probity-2-0/rover-hardware/jude-mechanical designs/rare wheel suspension.SLDASM

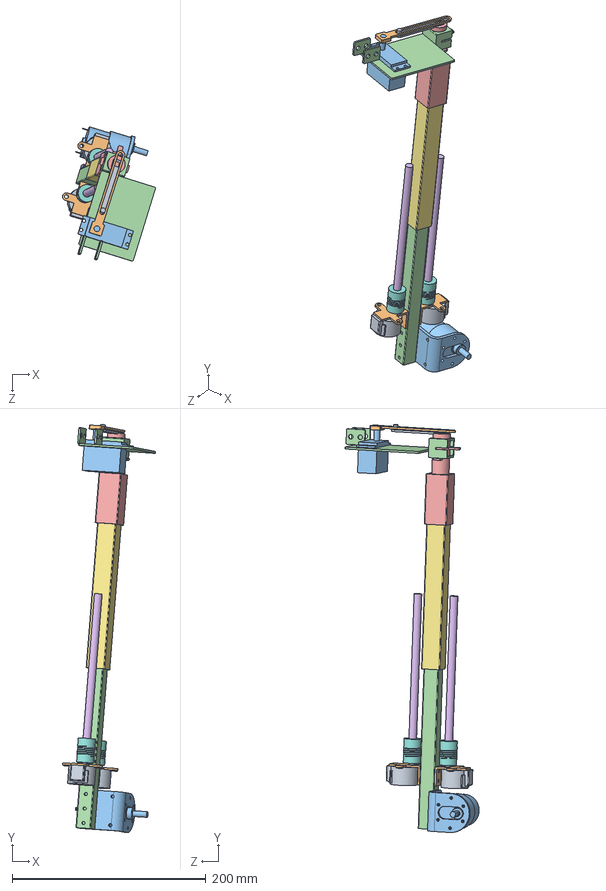
[picture p19: CAD file, 2026-03-30]
jude-mechanical designs/rare wheel suspension.SLDASM
96.2 x 421.2 x 138.8 mm
16mm inner tube
motor-bracket combined
suspension stepper bracket x 2
byj28--48 x 2
5to8 flexible coupler x 2
20mmsteel tube
suspension pin x 2
servo whee suspension connector cup
servo rotation strength fixture-rare
my_mg996r
slider pin
suspension rotary pin
