probity-2-0/rover-hardware/jude-mechanical designs/right full assembly.SLDASM

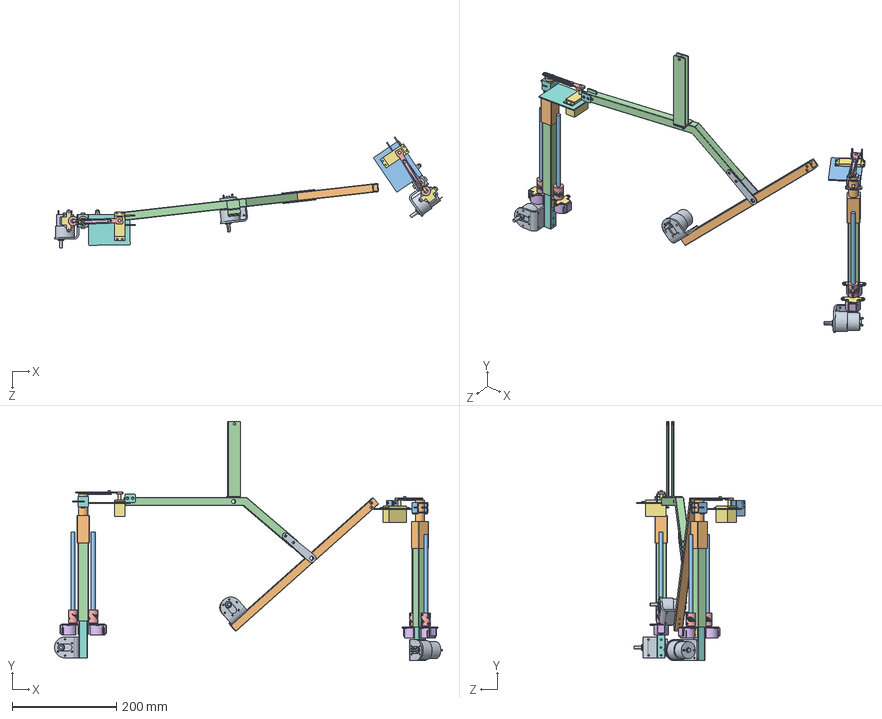
[picture p20: CAD file, 2026-03-30]
jude-mechanical designs/right full assembly.SLDASM
745.0 x 459.7 x 213.8 mm
16mm inner tube x 2
suspension stepper bracket x 4
byj28--48 x 4
5to8 flexible coupler x 4
20mmsteel tube x 2
suspension pin x 4
servo whee suspension connector cup x 2
motor-bracket combined x 3
servo rotation strength fixture-rare mirror
my_mg996r x 2
suspension rotary pin x 2
slider pin x 2
rare middle part mirror
servo rotation strength fixture mirror
middle16mm
connection bracket x 2
