probity-2-0/rover-hardware/jude-mechanical designs/assembled servo  system.SLDASM

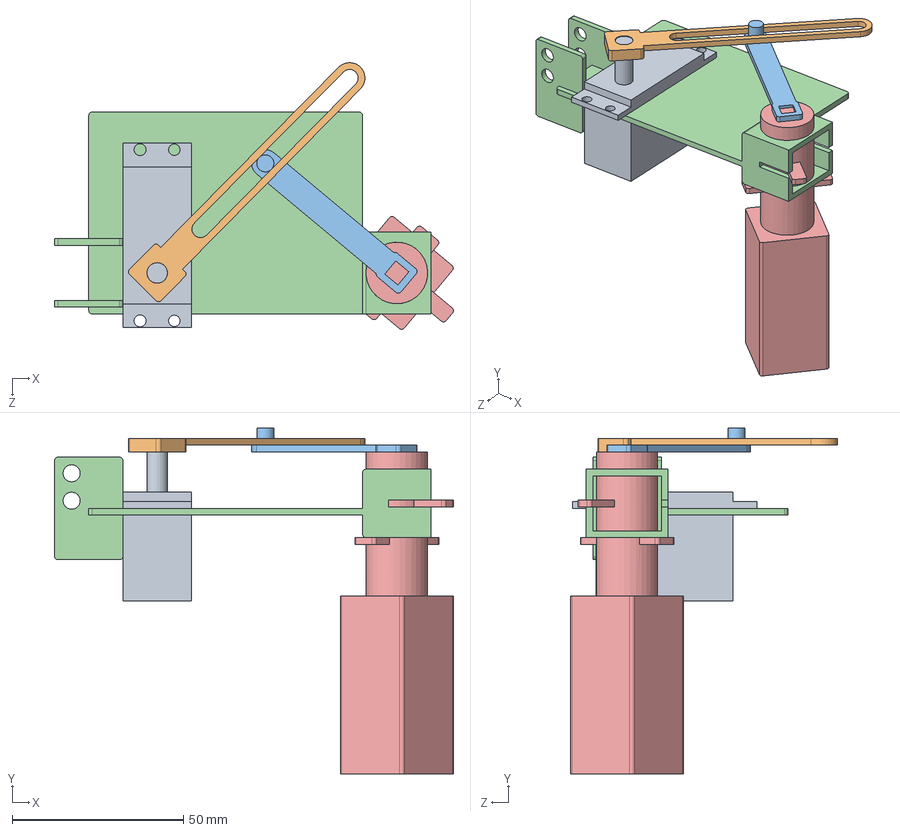
[picture p21: CAD file, 2026-03-30]
jude-mechanical designs/assembled servo system.SLDASM
116.6 x 101.0 x 77.9 mm
servo whee suspension connector cup
servo rotation strength fixture
suspension rotary pin
slider pin
my_mg996r
