probity-2-0/rover-hardware/jude-mechanical designs/middle16mm.SLDPRT

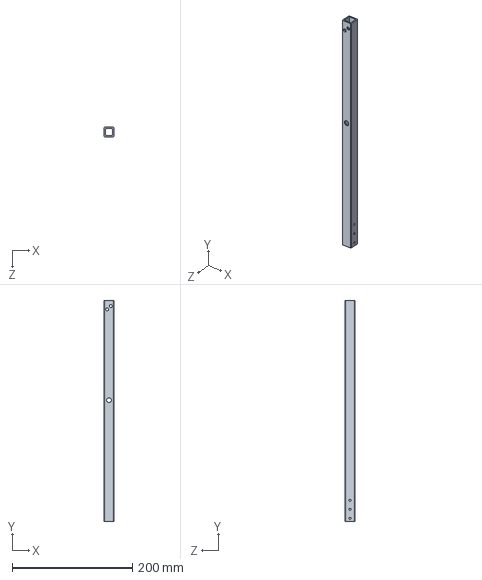
[picture p29: CAD file, 2026-03-30]
jude-mechanical designs/middle16mm.SLDPRT
16.0 x 368.0 x 16.0 mm
