probity-2-0/rover-hardware/jude-mechanical designs/JGB37-520-12v-319RPM.SLDPRT

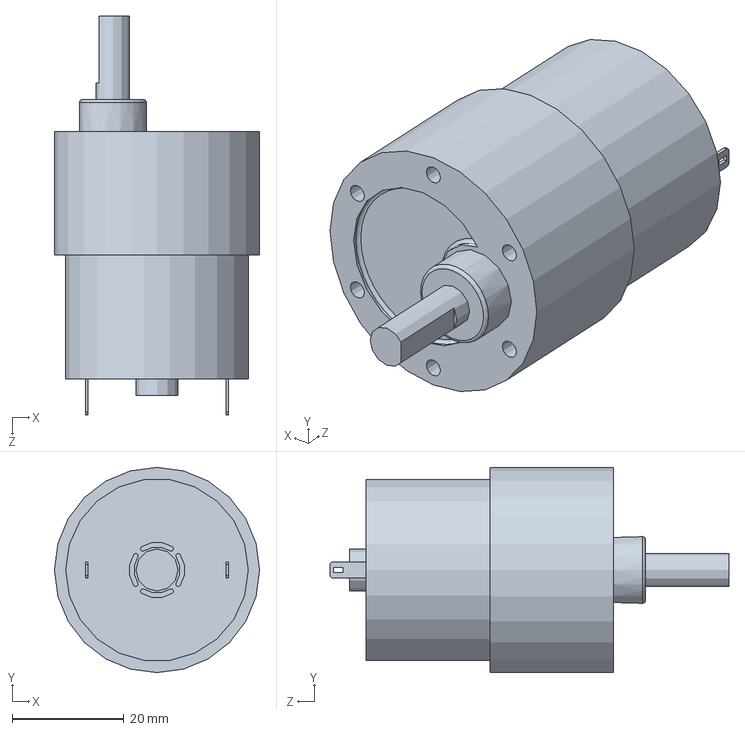
[picture p30: CAD file, 2026-03-30]
jude-mechanical designs/JGB37-520-12v-319RPM.SLDPRT
36.8 x 36.8 x 71.5 mm
