probity-2-0/rover-hardware/jude-mechanical designs/body width member.SLDPRT

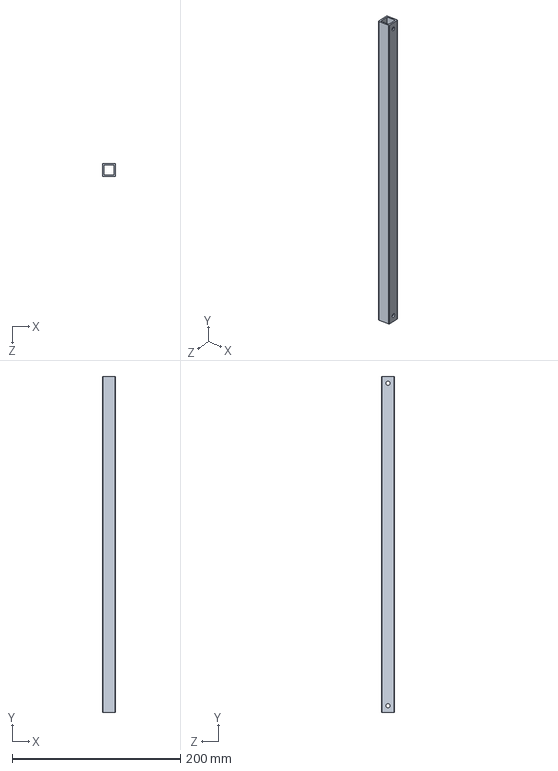
[picture p31: CAD file, 2026-03-30]
jude-mechanical designs/body width member.SLDPRT
16.0 x 400.0 x 16.0 mm
