probity-2-0/rover-hardware/jude-mechanical designs/suspension bracket.SLDPRT

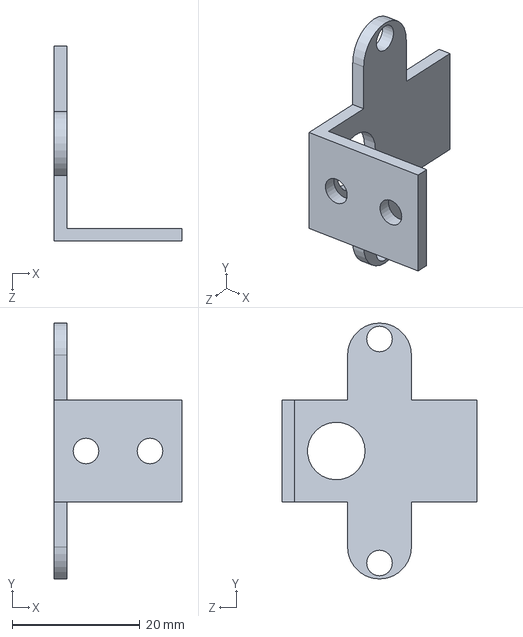
[picture p32: CAD file, 2026-03-30]
jude-mechanical designs/suspension bracket.SLDPRT
20.0 x 40.0 x 30.5 mm
