probity-2-0/rover-hardware/jude-mechanical designs/button  frame.SLDPRT

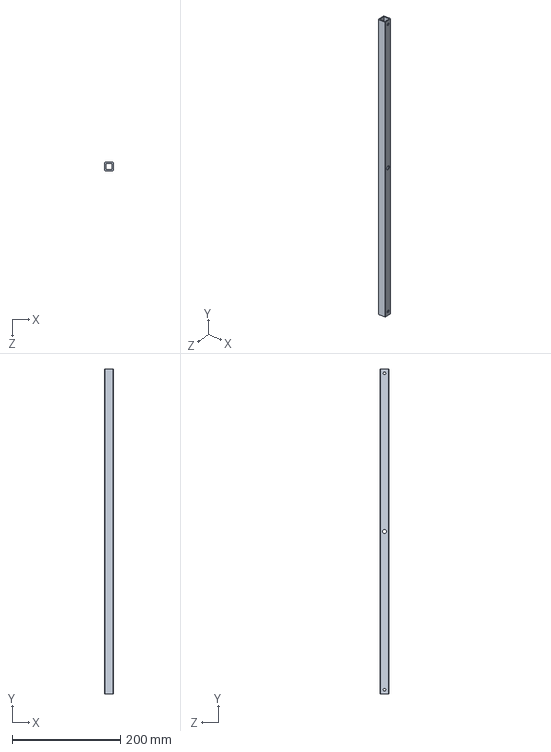
[picture p33: CAD file, 2026-03-30]
jude-mechanical designs/button frame.SLDPRT
16.0 x 600.0 x 16.0 mm
