probity-2-0/rover-hardware/jude-mechanical designs/tire mock up.SLDPRT

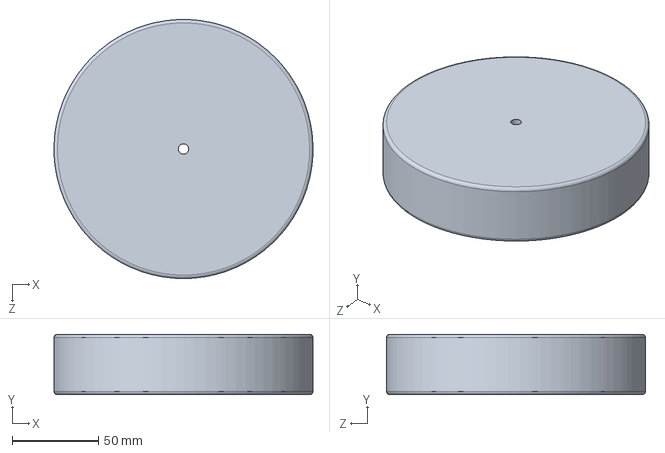
[picture p34: CAD file, 2026-03-30]
jude-mechanical designs/tire mock up.SLDPRT
150.0 x 35.0 x 150.0 mm
