probity-2-0/rover-hardware/jude-mechanical designs/servo whee suspension connector cup.SLDPRT

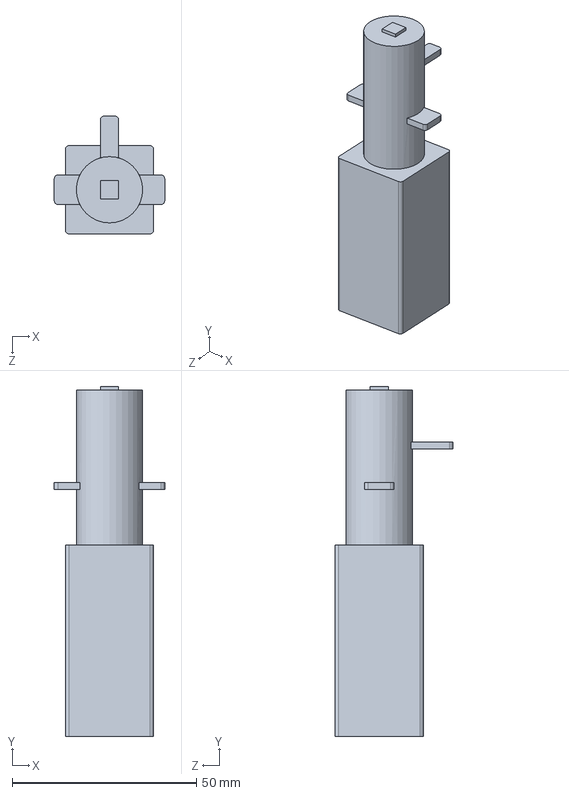
[picture p35: CAD file, 2026-03-30]
jude-mechanical designs/servo whee suspension connector cup.SLDPRT
30.0 x 95.0 x 32.0 mm
