probity-2-0/rover-hardware/jude-mechanical designs/motor-bracket combined.SLDPRT

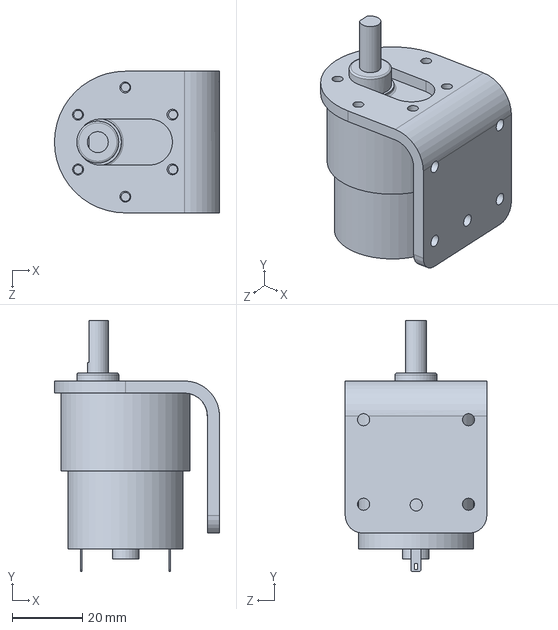
[picture p36: CAD file, 2026-03-30]
jude-mechanical designs/motor-bracket combined.SLDPRT
47.0 x 71.5 x 40.4 mm
