probity-2-0/rover-hardware/jude-mechanical designs/byj28--48.SLDPRT

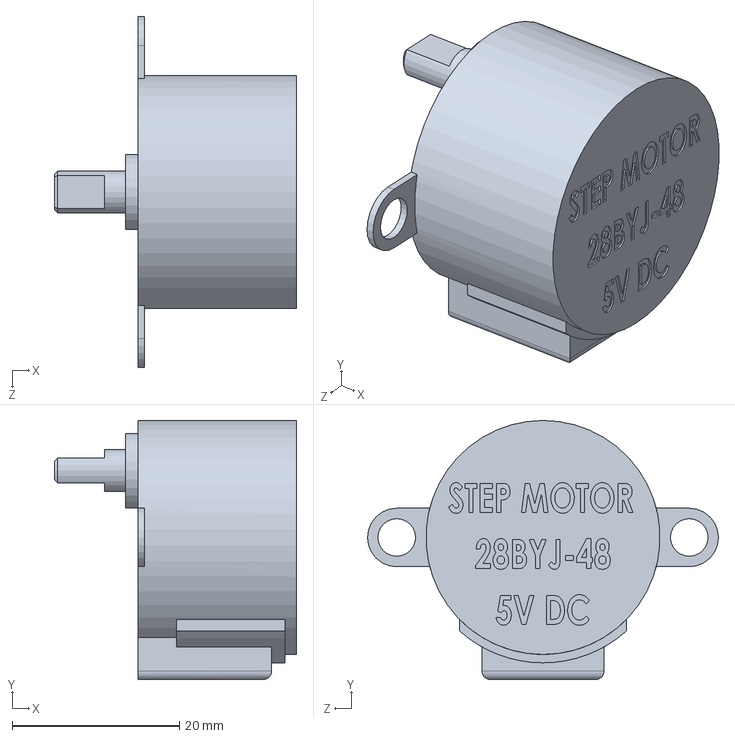
[picture p37: CAD file, 2026-03-30]
jude-mechanical designs/byj28--48.SLDPRT
29.0 x 31.0 x 42.0 mm
