probity-2-0/rover-hardware/jude-mechanical designs/bogie pin.SLDPRT

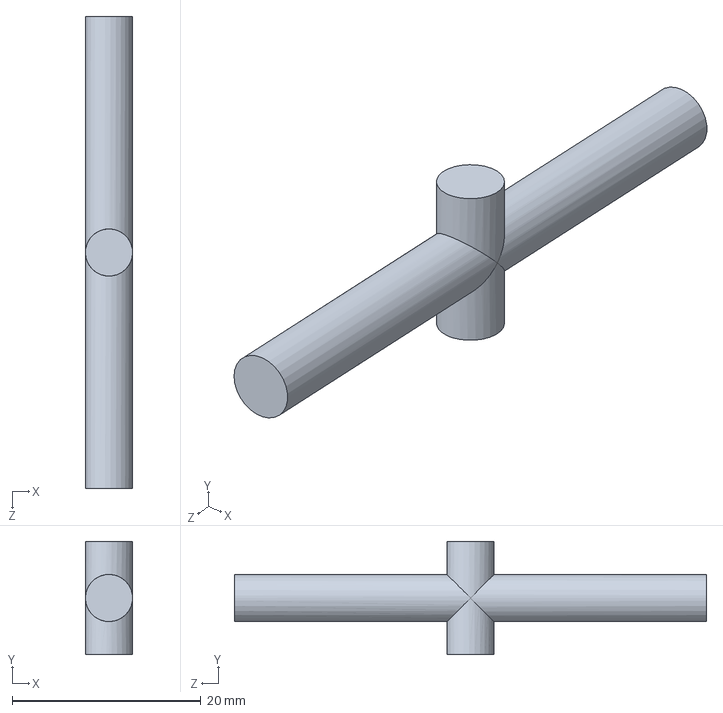
[picture p38: CAD file, 2026-03-30]
jude-mechanical designs/bogie pin.SLDPRT
5.00 x 12.0 x 50.0 mm
