probity-2-0/rover-hardware/jude-mechanical designs/SERVO ARM HORN 25T ALUMINIUM.SLDPRT

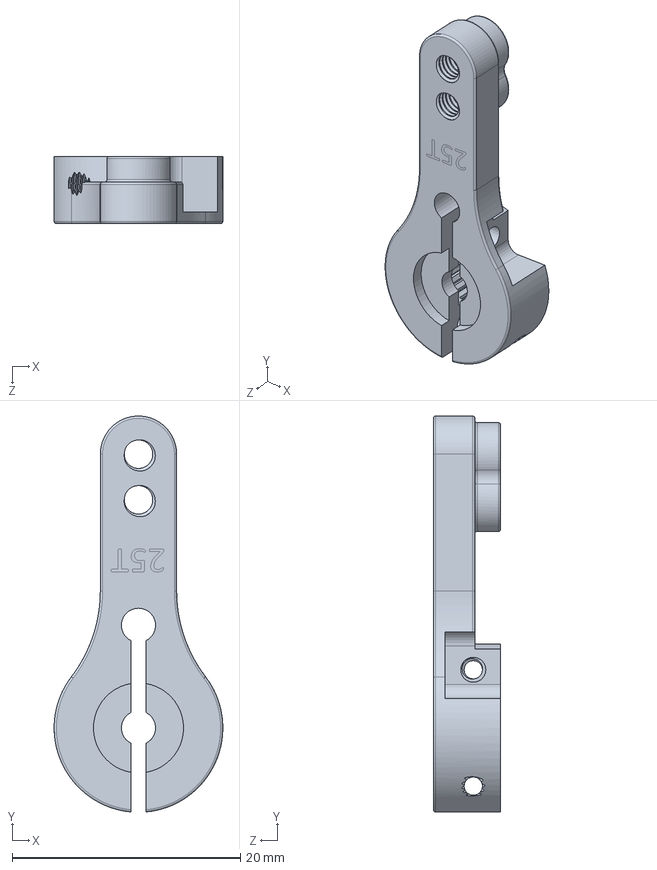
[picture p39: CAD file, 2026-03-30]
jude-mechanical designs/SERVO ARM HORN 25T ALUMINIUM.SLDPRT
14.8 x 34.7 x 5.90 mm
