probity-2-0/rover-hardware/jude-mechanical designs/top cross member.SLDPRT

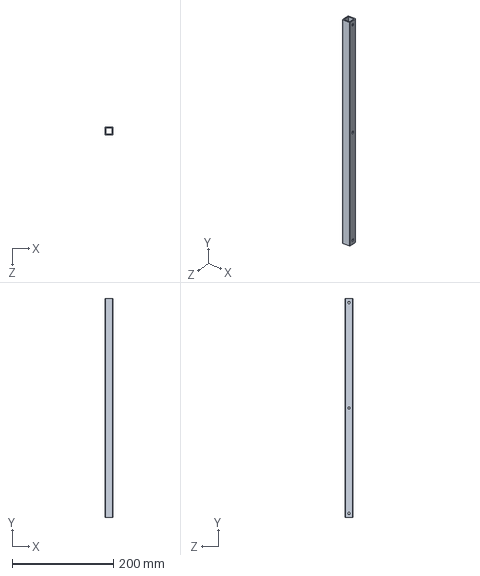
[picture p40: CAD file, 2026-03-30]
jude-mechanical designs/top cross member.SLDPRT
16.0 x 432.0 x 16.0 mm
