probity-2-0/rover-hardware/jude-mechanical designs/suspension stepper bracket.SLDPRT

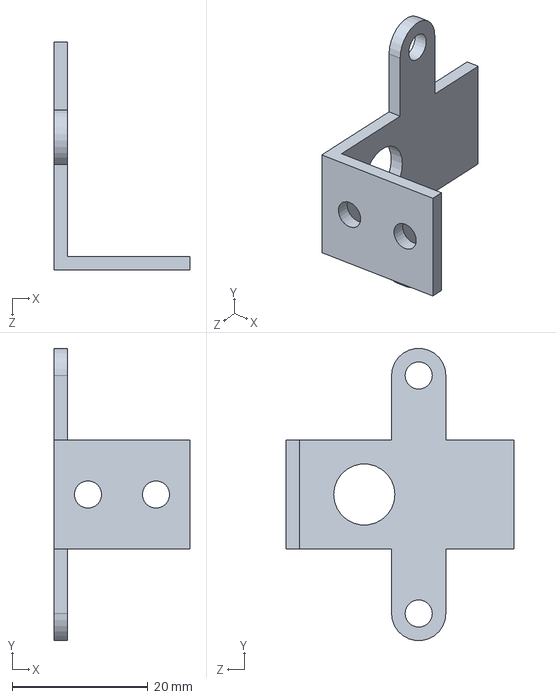
[picture p41: CAD file, 2026-03-30]
jude-mechanical designs/suspension stepper bracket.SLDPRT
20.0 x 42.9 x 33.5 mm
