probity-2-0/rover-hardware/jude-mechanical designs/slider pin.SLDPRT

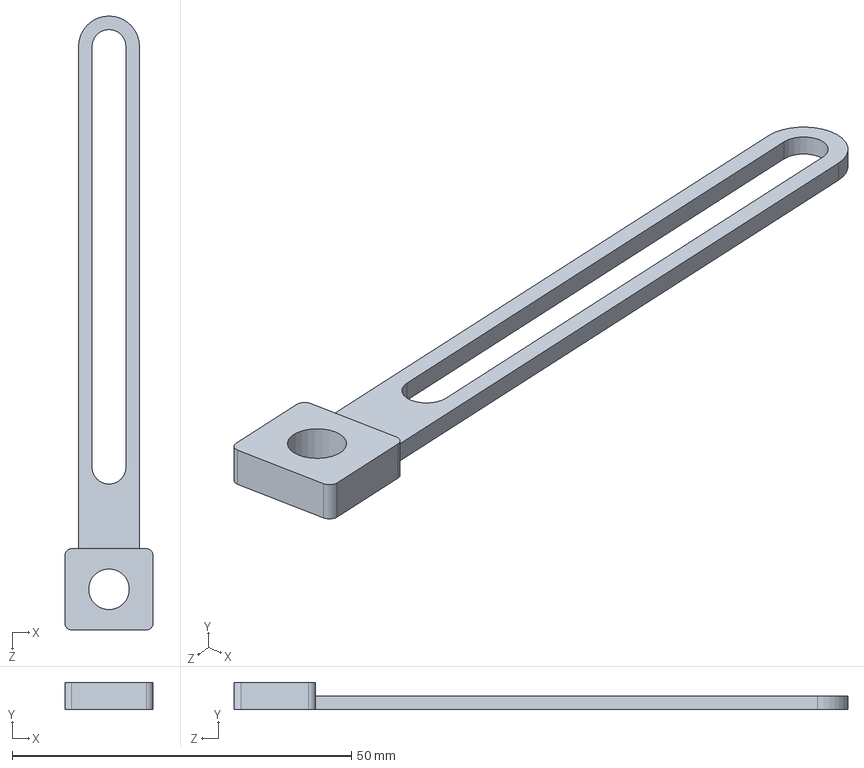
[picture p42: CAD file, 2026-03-30]
jude-mechanical designs/slider pin.SLDPRT
13.0 x 4.00 x 90.5 mm
