probity-2-0/rover-hardware/jude-mechanical designs/connection bracket.SLDPRT

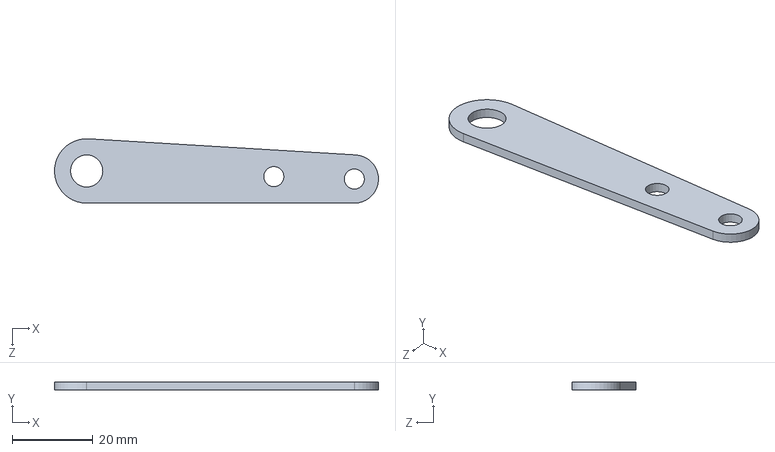
[picture p43: CAD file, 2026-03-30]
jude-mechanical designs/connection bracket.SLDPRT
80.5 x 2.00 x 16.0 mm
