probity-2-0/rover-hardware/jude-mechanical designs/5to8 flexible coupler.SLDPRT

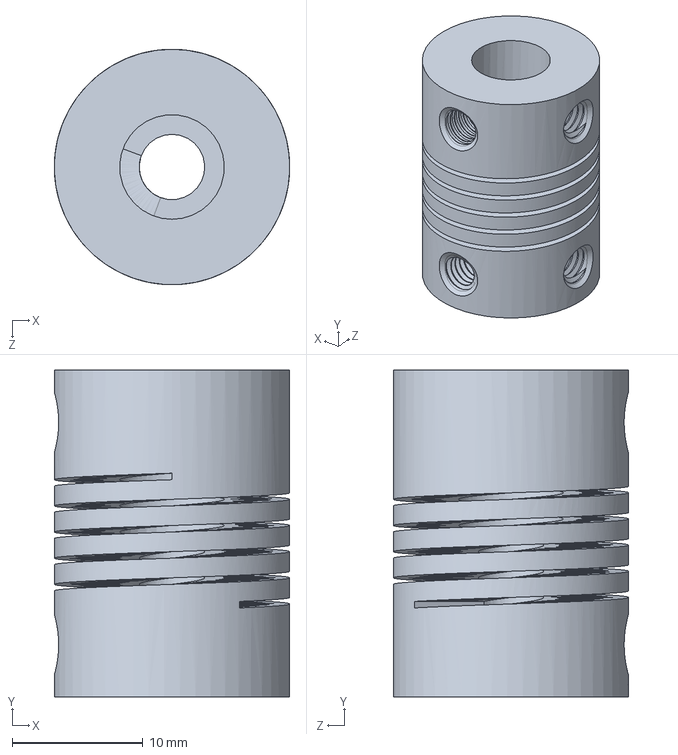
[picture p44: CAD file, 2026-03-30]
jude-mechanical designs/5to8 flexible coupler.SLDPRT
18.0 x 25.0 x 18.0 mm
