probity-2-0/rover-hardware/jude-mechanical designs/suspension pin.SLDPRT

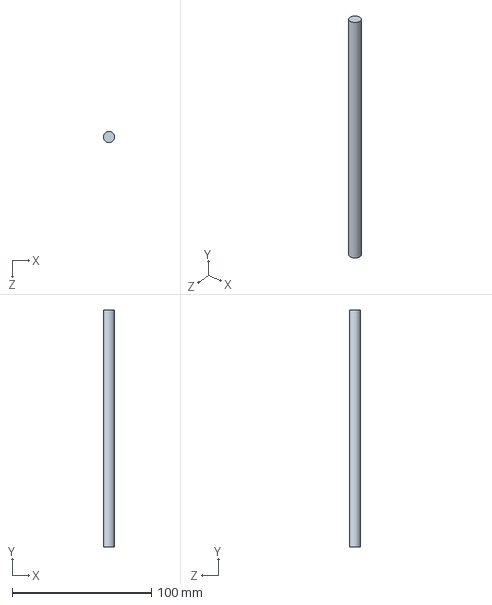
[picture p45: CAD file, 2026-03-30]
jude-mechanical designs/suspension pin.SLDPRT
7.99 x 170.0 x 8.00 mm
