probity-2-0/rover-hardware/jude-mechanical designs/JGB37-520 12 v metal geared motor bracket.SLDPRT

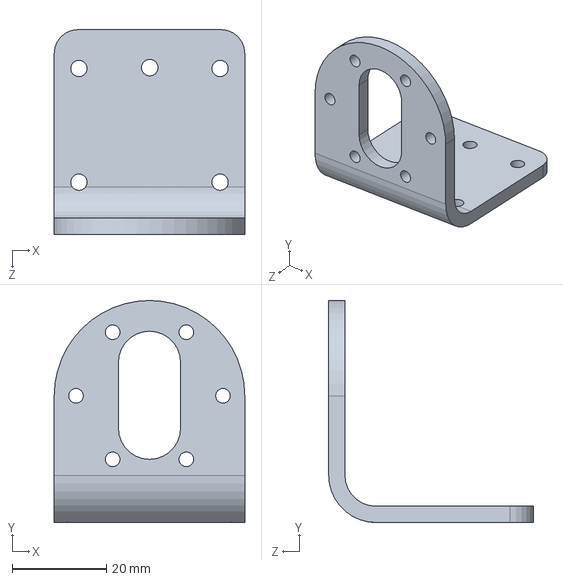
[picture p46: CAD file, 2026-03-30]
jude-mechanical designs/JGB37-520 12 v metal geared motor bracket.SLDPRT
40.3 x 47.0 x 43.3 mm
