probity-2-0/rover-hardware/jude-mechanical designs/connector pin.SLDPRT

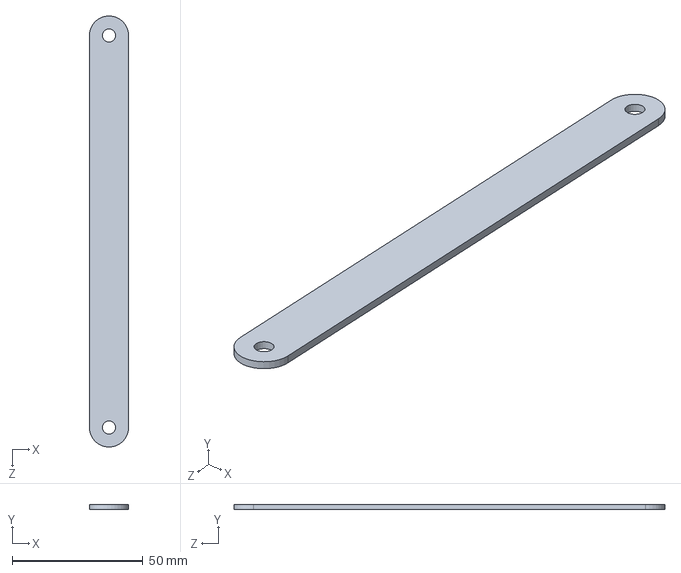
[picture p47: CAD file, 2026-03-30]
jude-mechanical designs/connector pin.SLDPRT
15.0 x 2.00 x 164.9 mm
