probity-2-0/rover-hardware/jude-mechanical designs/20mmsteel tube.SLDPRT

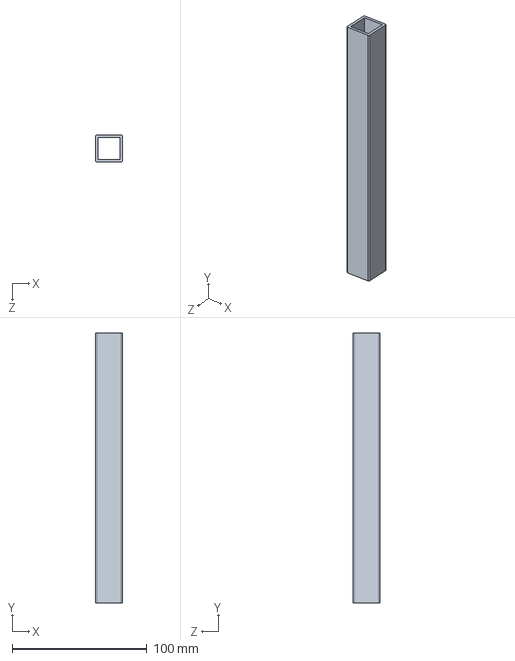
[picture p48: CAD file, 2026-03-30]
jude-mechanical designs/20mmsteel tube.SLDPRT
20.0 x 200.0 x 20.0 mm
