probity-2-0/rover-hardware/jude-mechanical designs/boggie.SLDPRT

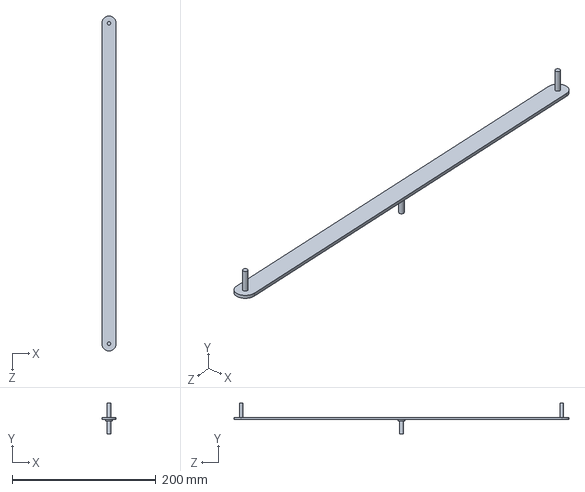
[picture p49: CAD file, 2026-03-30]
jude-mechanical designs/boggie.SLDPRT
20.0 x 43.0 x 466.0 mm
