probity-2-0/rover-hardware/jude-mechanical designs/suspension rotary pin.SLDPRT

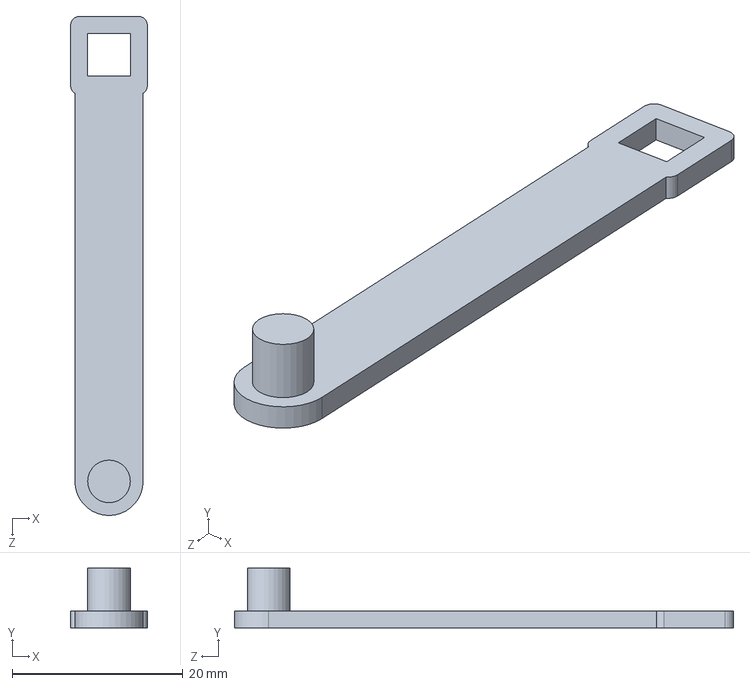
[picture p50: CAD file, 2026-03-30]
jude-mechanical designs/suspension rotary pin.SLDPRT
9.00 x 7.00 x 58.5 mm
